andresv/industrial-switcher/firmware/src/ntctable.h

#ifndef NTCTABLE_H
#define NTCTABLE_H

#define NUMTEMPS 103 // NTC table

// https://raw.github.com/reprap/firmware/master/createTemperatureLookup.py
// python createTemperatureLookup.py --r0=4700 --t0=25 --r1=0 --r2=1000 --beta=3950 --max-adc=1023
// num steps were manualy set to 100 and adcref to 3.6 V
// http://hydraraptor.blogspot.com/2007/10/measuring-temperature-easy-way.html
// NTC 4.7k EPCOS B57045-K472-K

const short temptable[NUMTEMPS][2] = {
   {1, 554},
   {11, 277},
   {21, 231},
   {31, 206},
   {41, 190},
   {51, 178},
   {61, 168},
   {71, 160},
   {81, 154},
   {91, 148},
   {101, 143},
   {111, 138},
   {121, 134},
   {131, 130},
   {141, 127},
   {151, 123},
   {161, 120},
   {171, 118},
   {181, 115},
   {191, 113},
   {201, 110},
   {211, 108},
   {221, 106},
   {231, 104},
   {241, 102},
   {251, 100},
   {261, 98},
   {271, 96},
   {281, 95},
   {291, 93},
   {301, 91},
   {311, 90},
   {321, 88},
   {331, 87},
   {341, 85},
   {351, 84},
   {361, 82},
   {371, 81},
   {381, 80},
   {391, 78},
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
};

#endif
